Xyl2k/TSA-Travel-Sentry-master-keys/IGES/TSA007.IGS

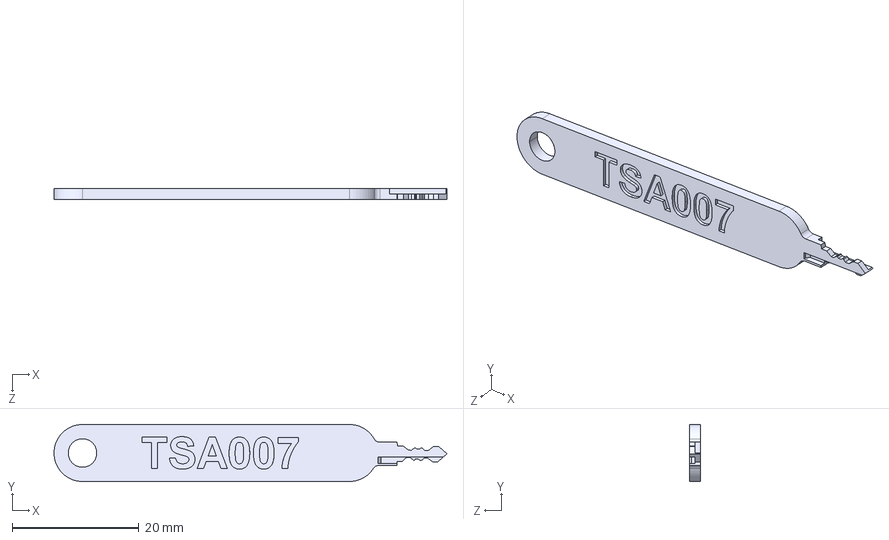
[picture p17: CAD file, 2015-09-10]
IGES/TSA007.IGS
62.1 x 9.00 x 1.75 mm
