Xyl2k/TSA-Travel-Sentry-master-keys/TSA007_stubby.stl

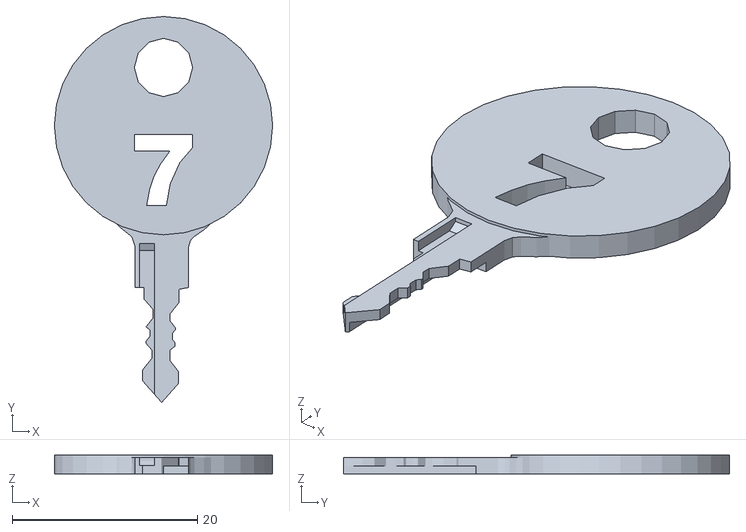
[picture p18: CAD file, 2015-09-13]
TSA007_stubby.stl
23.6 x 41.6 x 2.01
